ppw0021/Gyro_Gauntlet/PCB Files/CNC Standard/iCloud Photos/iCloud Photos/IMG_5190.JPEG

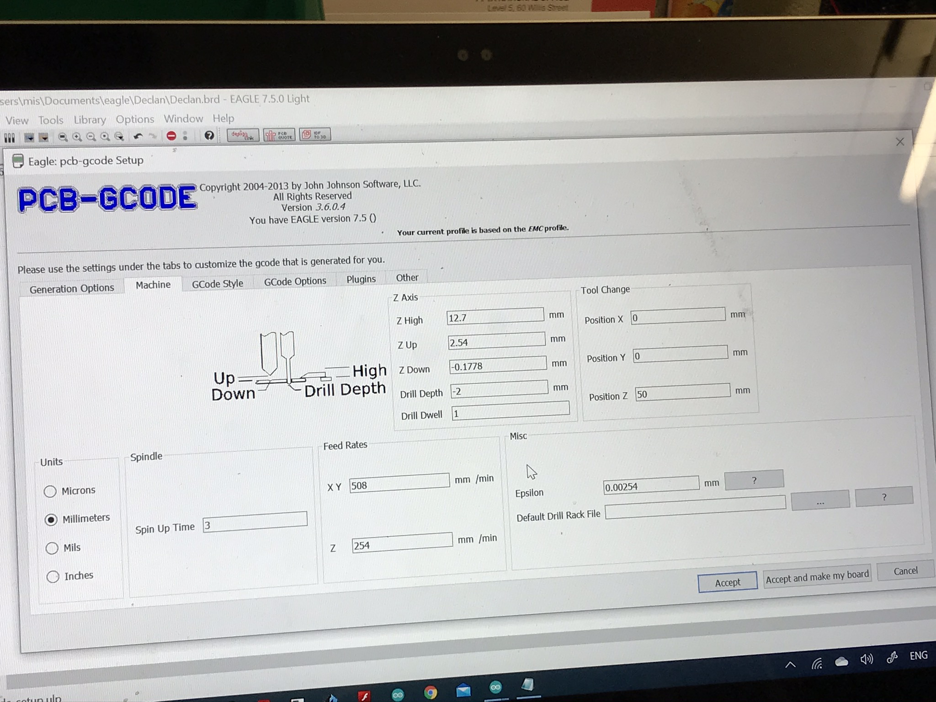
PCB Files/CNC Standard/iCloud Photos/iCloud Photos/IMG_5190.JPEG
